ft-13/Picture-Frame-with-ESP32-and-Camera/Software/2_pic_converter/converter/color_palette.JPG

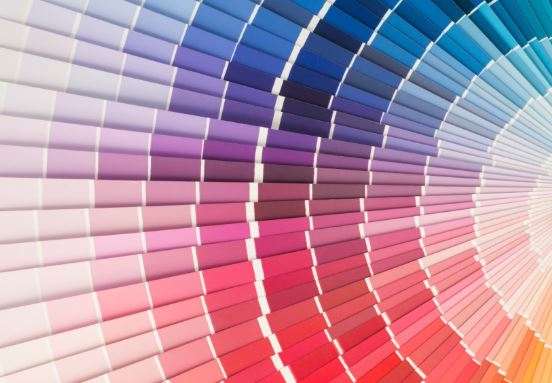
Software/2_pic_converter/converter/color_palette.JPG
